thegalaxykat/Smart-Dehumidifier/ESP8266-Program/credentials_TEMPLATE.h

#ifndef CREDENTIALS_H
#define CREDENTIALS_H

// WiFi credentials
#define STASSID "your-wifi-name"
#define STAPSK "your-wifi-password"

// Smart Plug IP
#define RELAYIP "192.168.33.1"  // Replace with your Shelly plug IP (this is the default)

#endif
